otvam/transformer_MF_MV_25kW/step/top_spacer.ipt.stp

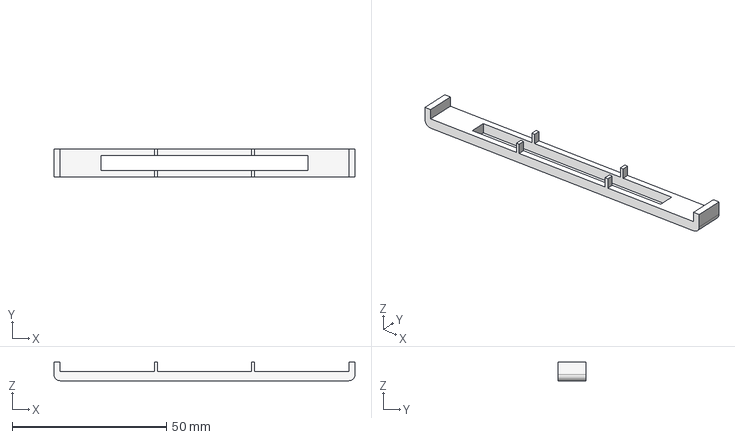
[picture p17: CAD file, 2025-02-24]
step/top_spacer.ipt.stp
97.5 x 9.00 x 6.00 mm
