otvam/transformer_MF_MV_25kW/step/core_earth.ipt.stp

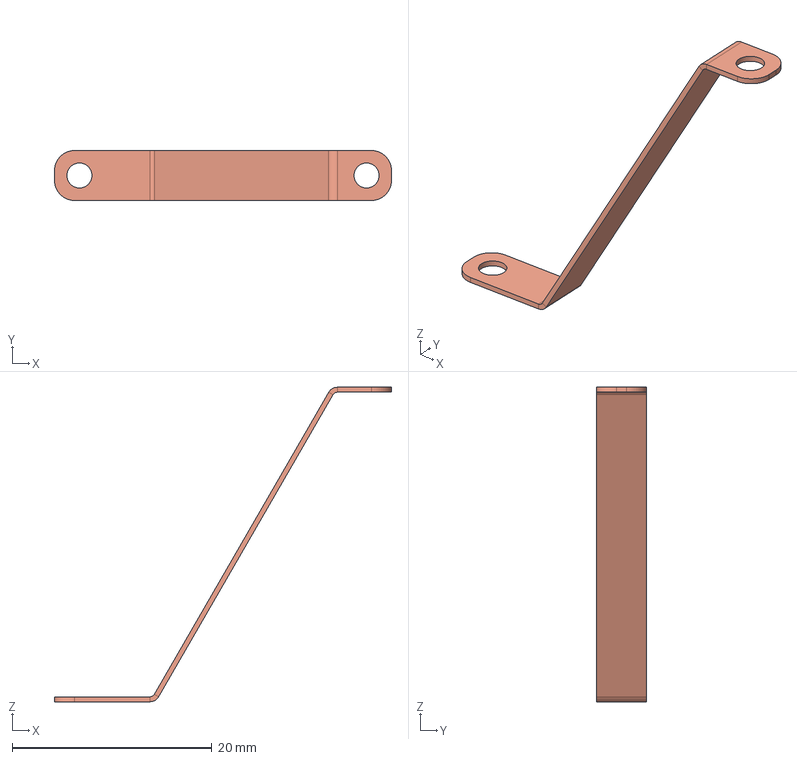
[picture p18: CAD file, 2025-02-24]
step/core_earth.ipt.stp
33.7 x 5.00 x 31.5 mm
