otvam/transformer_MF_MV_25kW/step/plate_out.ipt.stp

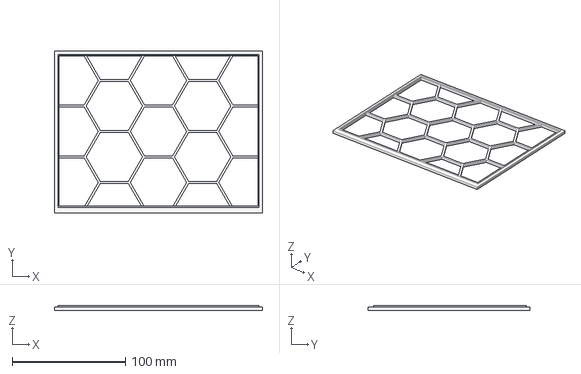
[picture p19: CAD file, 2025-02-24]
step/plate_out.ipt.stp
183.5 x 143.0 x 4.00 mm
