otvam/transformer_MF_MV_25kW/step/termination_closing.ipt.stp

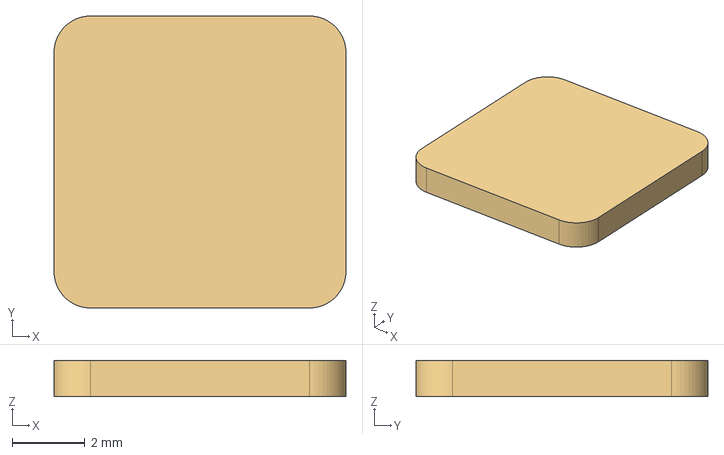
[picture p20: CAD file, 2025-02-24]
step/termination_closing.ipt.stp
8.00 x 8.00 x 1.00 mm
