otvam/transformer_MF_MV_25kW/step/coil_former_mold.ipt.stp

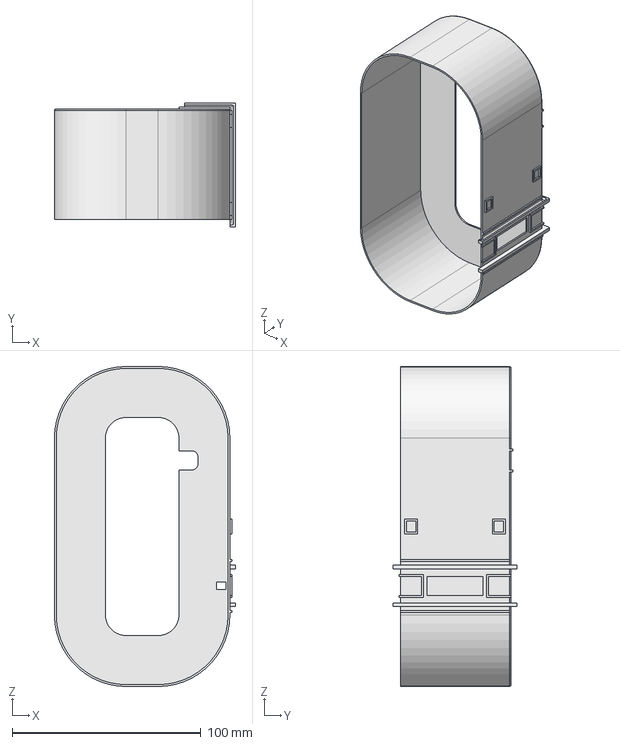
[picture p21: CAD file, 2025-02-24]
step/coil_former_mold.ipt.stp
96.0 x 65.5 x 169.5 mm
