otvam/transformer_MF_MV_25kW/step/top_conductor.ipt.stp

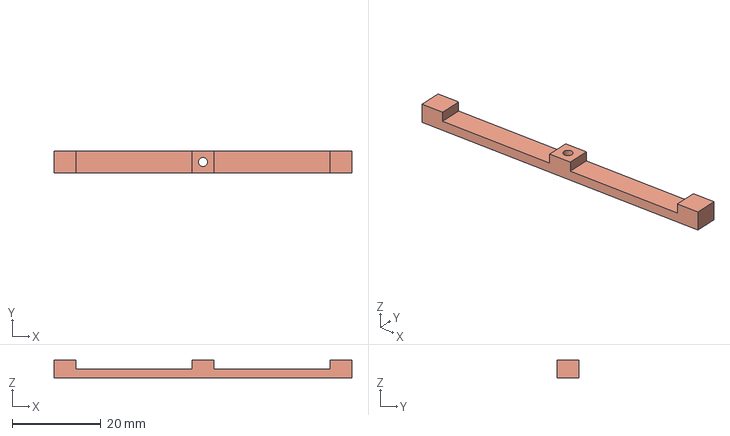
[picture p22: CAD file, 2025-02-24]
step/top_conductor.ipt.stp
67.0 x 5.00 x 4.00 mm
