otvam/transformer_MF_MV_25kW/step/temperature_cover.ipt.stp

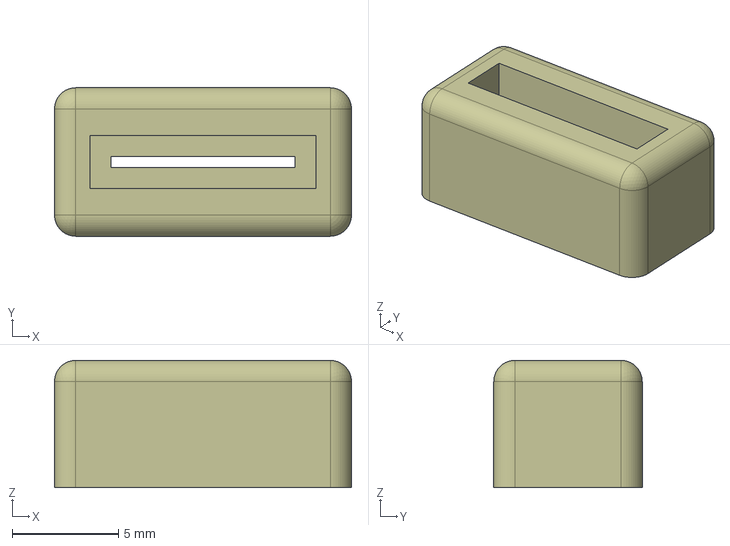
[picture p23: CAD file, 2025-02-24]
step/temperature_cover.ipt.stp
14.0 x 7.00 x 6.00 mm
