otvam/transformer_MF_MV_25kW/drawing/3d_print/termination_lv_insulation.pdf

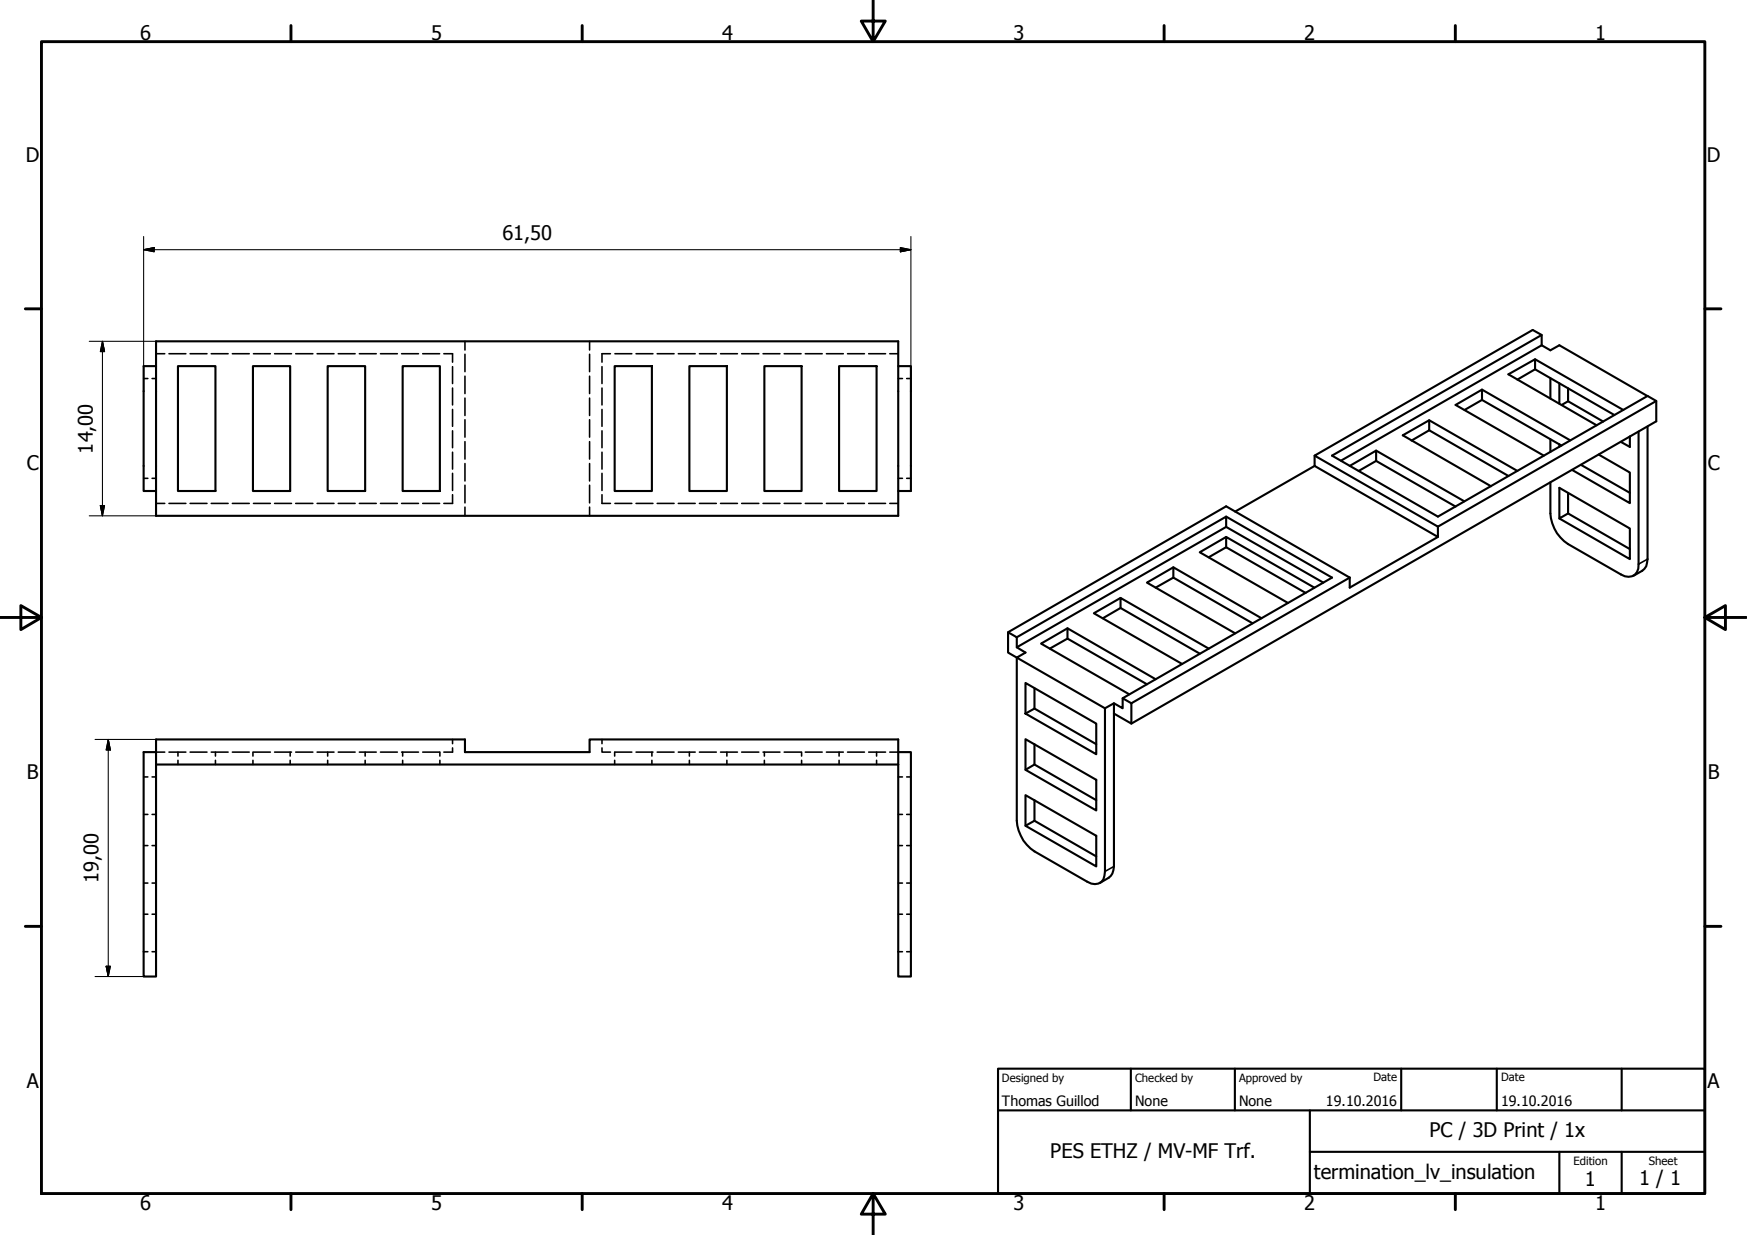
[picture p33: page 1]
PC / 3D Print / 1x; termination_lv_insulation; Thomas Guillod; None; Designed by; Checked by; Approved by; Date; Edition; Sheet

PES ETHZ / MV-MF Trf.
