otvam/transformer_MF_MV_25kW/drawing/transformer_all.pdf

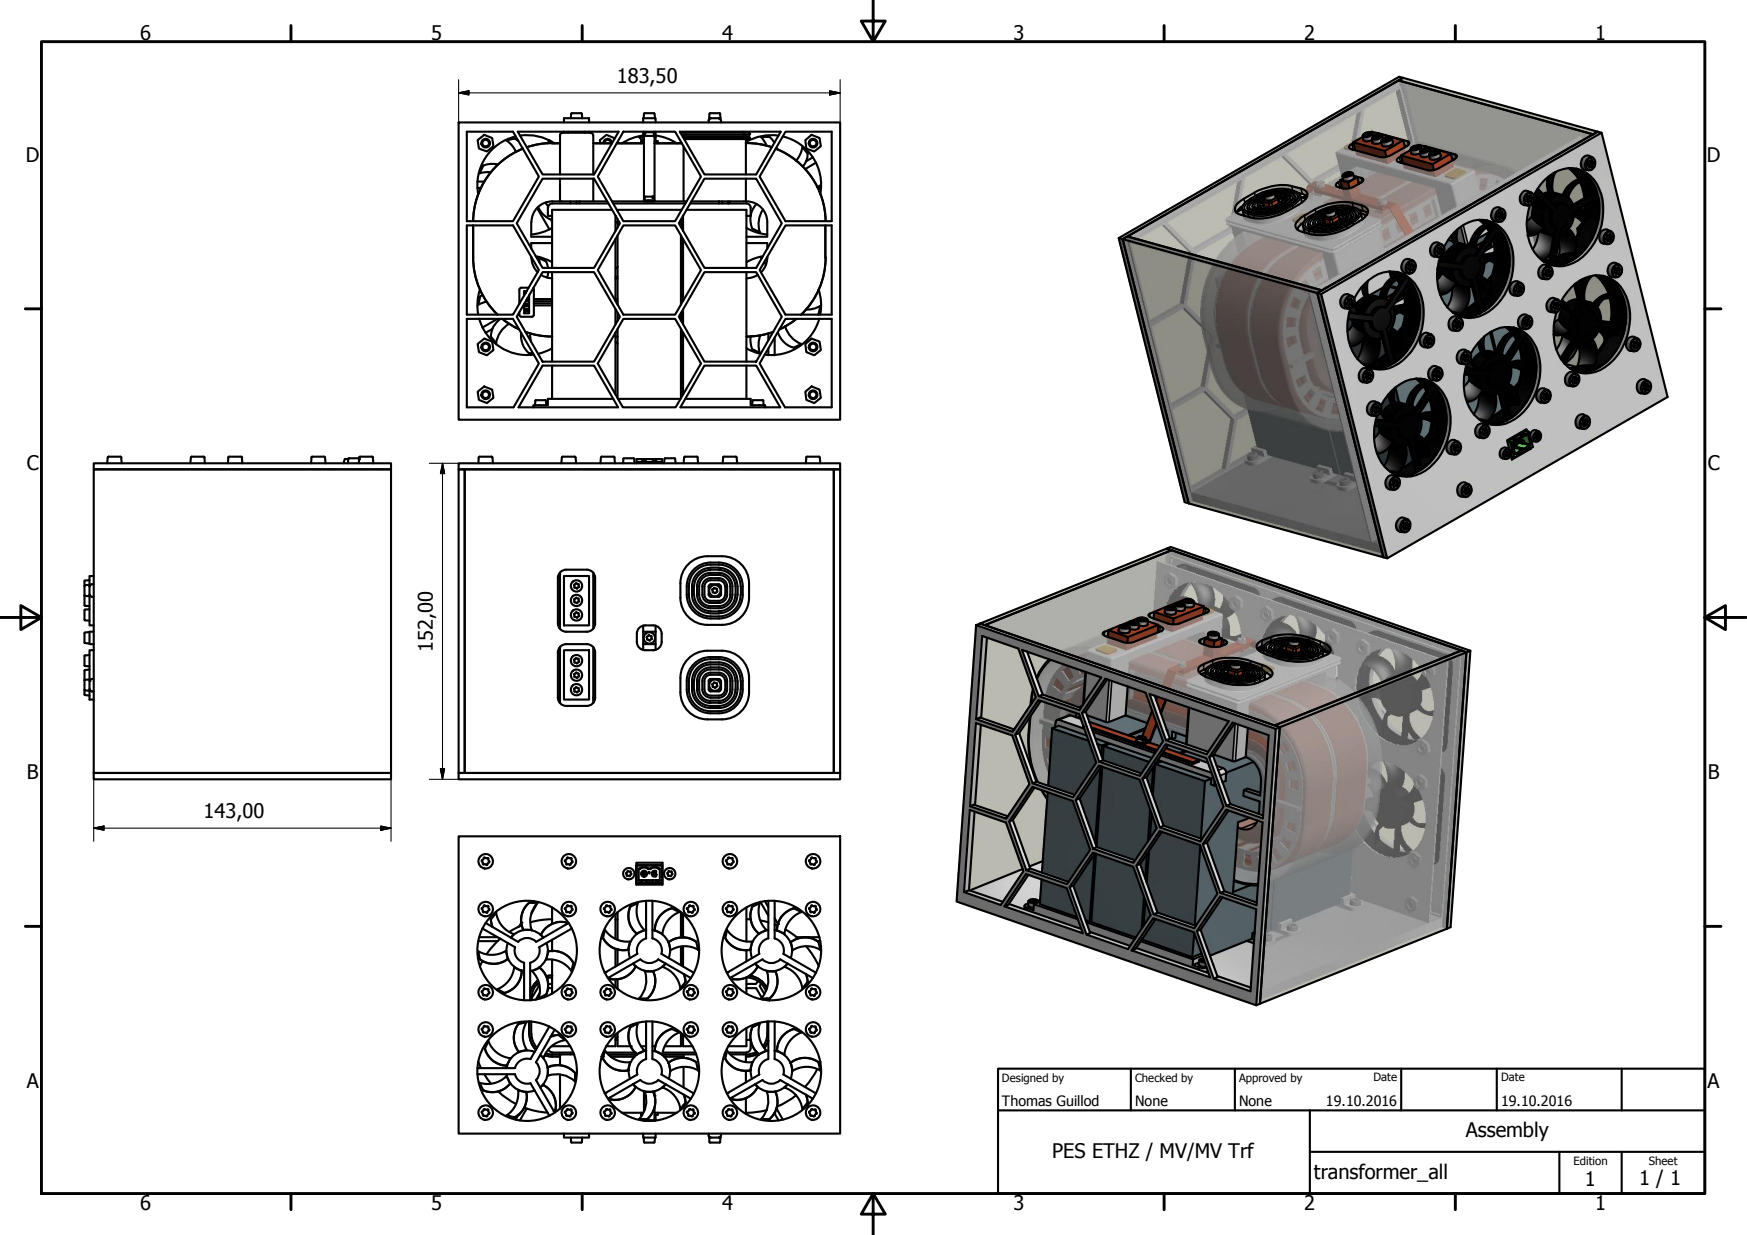
[picture p34: page 1]
Assembly; transformer_all; Thomas Guillod; None; Designed by; Checked by; Approved by; Date; Edition; Sheet

PES ETHZ / MV/MV Trf
