otvam/transformer_MF_MV_25kW/drawing/copper/termination_hv_conductor.pdf

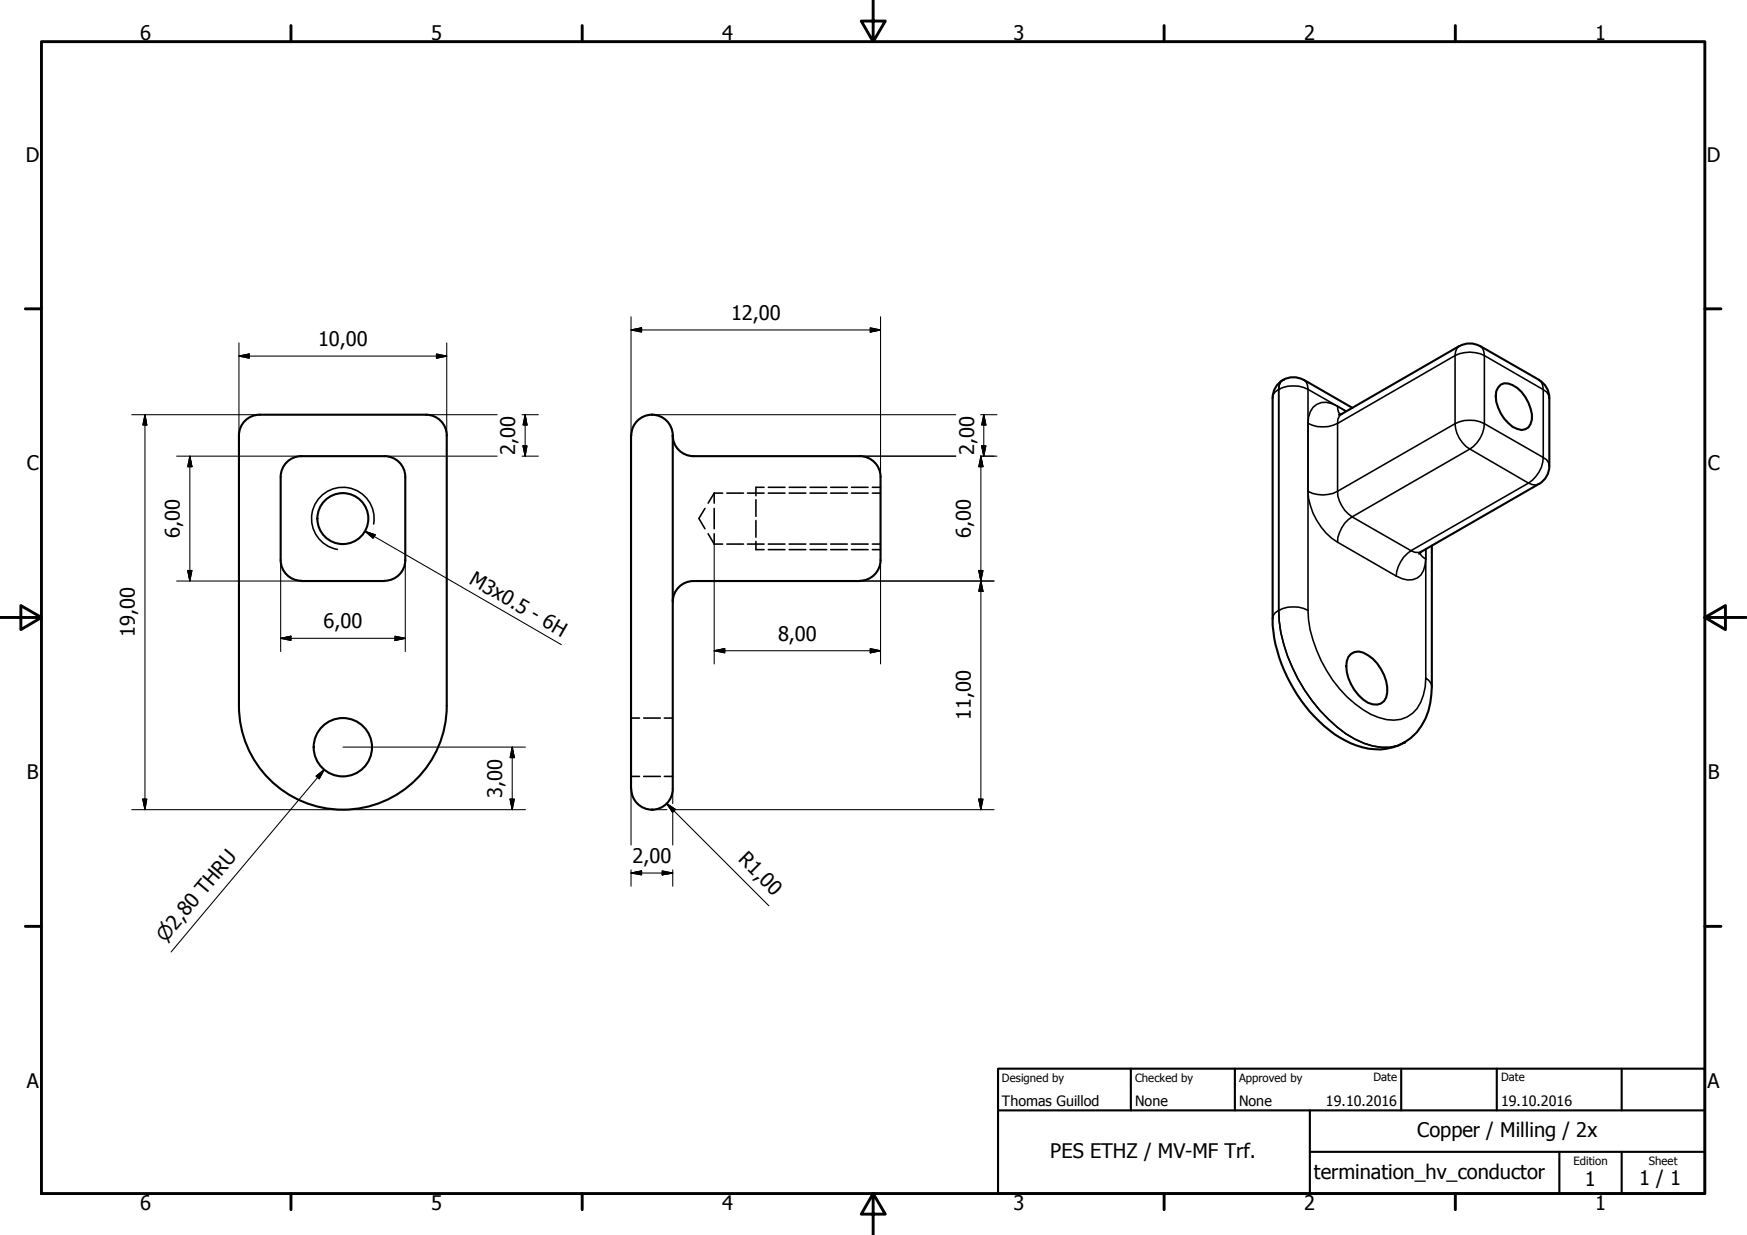
[picture p35: page 1]
Copper / Milling / 2x; termination_hv_conductor; Thomas Guillod; None; Designed by; Checked by; Approved by; Date; Edition; Sheet; P2,80 THRU

PES ETHZ / MV-MF Trf.
